barbeque/pico-rgbi-to-vga/firmware/src/include.h

// ****************************************************************************
//                                 
//                              Common definitions
//
// ****************************************************************************

// ----------------------------------------------------------------------------
//                                   Includes
// ----------------------------------------------------------------------------

#include "vendor/picovga/global.h"	// global common definitions
#include "generated/vga.pio.h"	// VGA PIO compilation

typedef float real;

// main
#include "main.h"		// main code
